inn-goose/eeprom-programmer/diagram/eeprom_programmer/eeprom_programmer.kicad_sch

## KiCad design diagram/eeprom_programmer/eeprom_programmer.kicad_sch (2025-11-06)

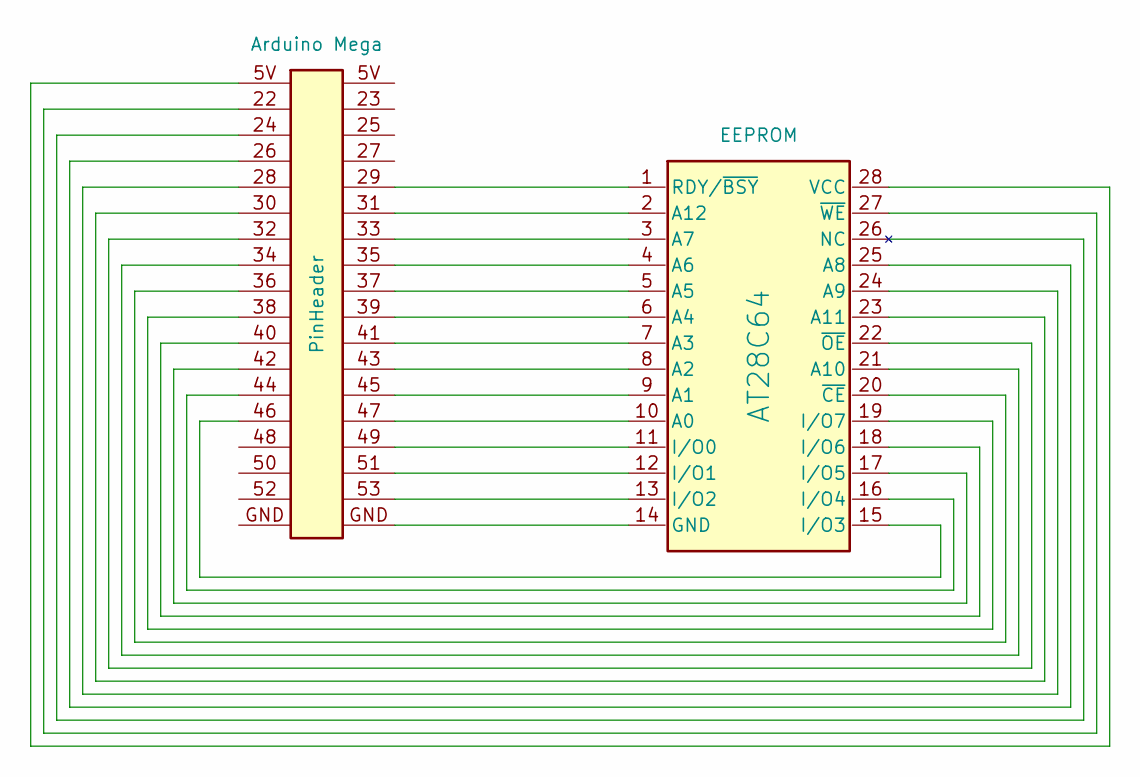
[picture p2: schematic eeprom_programmer.kicad_sch]

Parts:
AT28C64: EEPROM
PinHeader: Arduino Mega

Connections:
unnamed: AT28C64.1 (RDY/~BSY), PinHeader.29
unnamed: AT28C64.2 (A12), PinHeader.31
unnamed: AT28C64.3 (A7), PinHeader.33
unnamed: AT28C64.4 (A6), PinHeader.35
unnamed: AT28C64.5 (A5), PinHeader.37
unnamed: AT28C64.6 (A4), PinHeader.39
unnamed: AT28C64.7 (A3), PinHeader.41
unnamed: AT28C64.8 (A2), PinHeader.43
unnamed: AT28C64.9 (A1), PinHeader.45
unnamed: AT28C64.10 (A0), PinHeader.47
unnamed: AT28C64.11 (I/O0), PinHeader.49
unnamed: AT28C64.12 (I/O1), PinHeader.51
unnamed: AT28C64.13 (I/O2), PinHeader.53
unnamed: AT28C64.14 (GND), PinHeader.GND
unnamed: AT28C64.15 (I/O3), PinHeader.46
unnamed: AT28C64.16 (I/O4), PinHeader.44
unnamed: AT28C64.17 (I/O5), PinHeader.42
unnamed: AT28C64.18 (I/O6), PinHeader.40
unnamed: AT28C64.19 (I/O7), PinHeader.38
unnamed: AT28C64.20 (~CE), PinHeader.36
unnamed: AT28C64.21 (A10), PinHeader.34
unnamed: AT28C64.22 (~OE), PinHeader.32
unnamed: AT28C64.23 (A11), PinHeader.30
unnamed: AT28C64.24 (A9), PinHeader.28
unnamed: AT28C64.25 (A8), PinHeader.26
unnamed: AT28C64.26 (NC), PinHeader.24
unnamed: AT28C64.27 (~WE), PinHeader.22
unnamed: AT28C64.28 (VCC), PinHeader.5V
